DavidCas24/Adaptive_Telework_Environment/HARDWARE/Prototipo.png

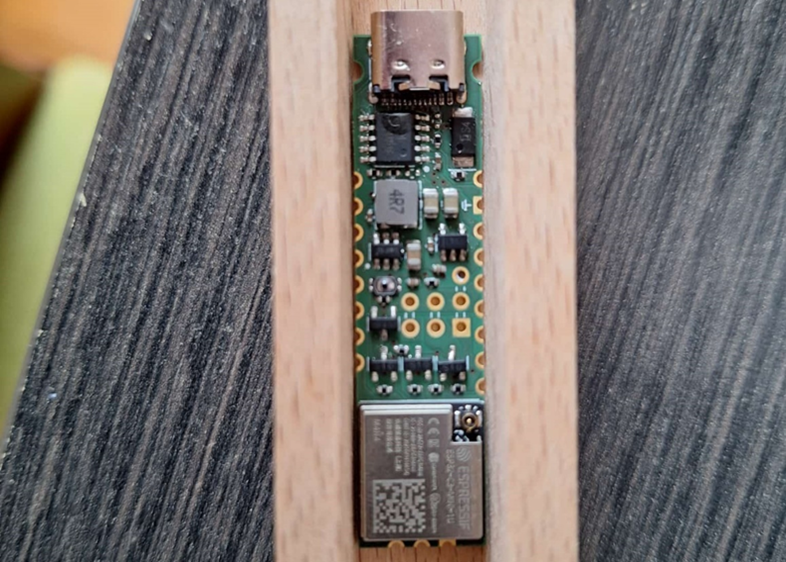
HARDWARE/Prototipo.png
