DavidCas24/Adaptive_Telework_Environment/PCB/3D/3D.png

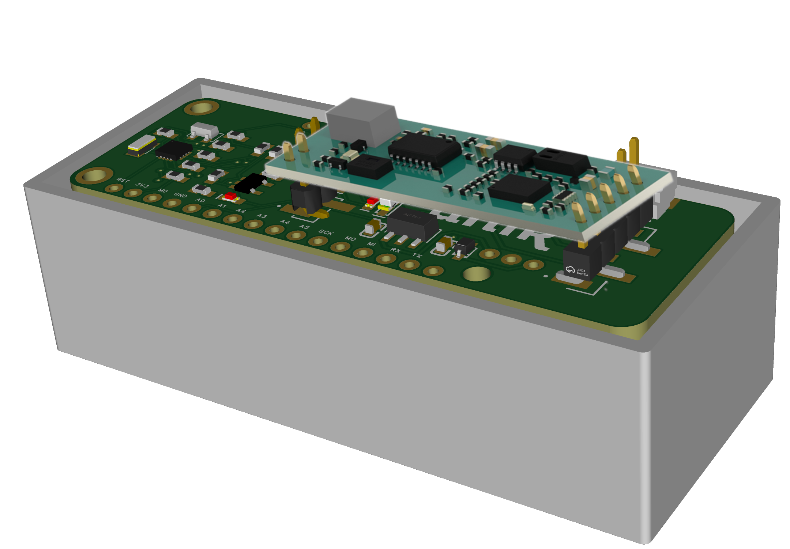
PCB/3D/3D.png
