DavidCas24/Adaptive_Telework_Environment/PCB/3D/3D_PCB_FeatherAB1805-SC_FINAL_2_2025-06-03_2025-06-03.png

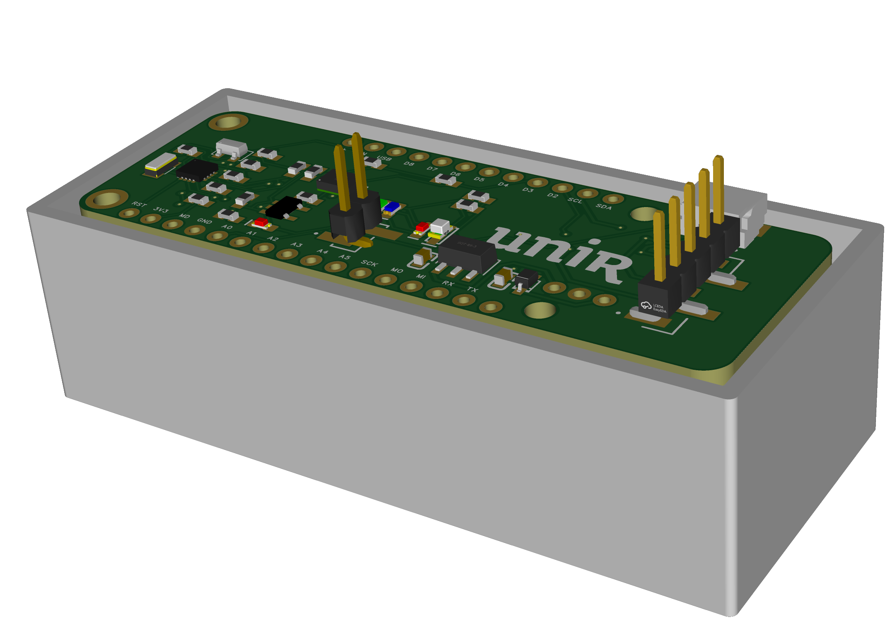
PCB/3D/3D_PCB_FeatherAB1805-SC_FINAL_2_2025-06-03_2025-06-03.png
