DavidCas24/Adaptive_Telework_Environment/PCB/3D/Ambimate - copia.png

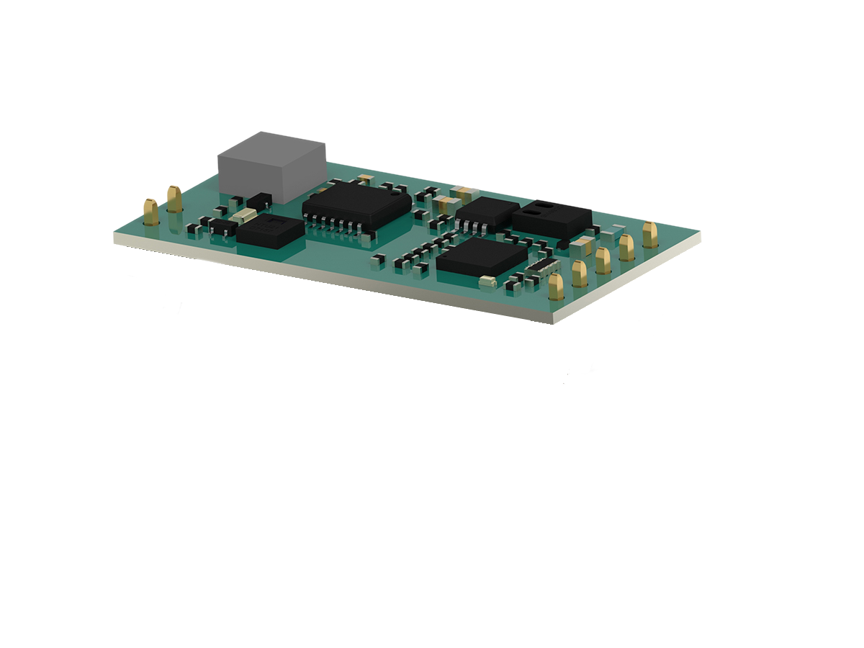
PCB/3D/Ambimate - copia.png
