DavidCas24/Adaptive_Telework_Environment/PCB/3D/PCB con envolvente.png

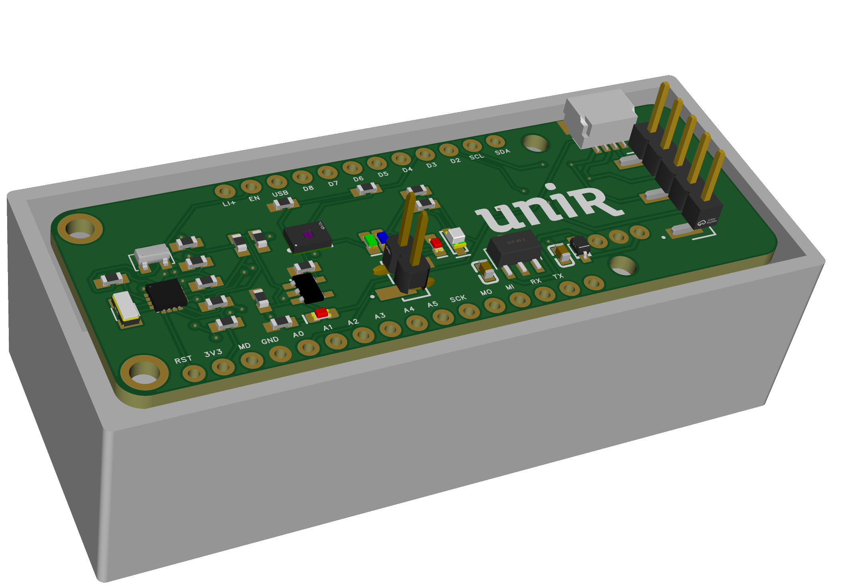
PCB/3D/PCB con envolvente.png
