DavidCas24/Adaptive_Telework_Environment/PCB/PARTICLE.IO SENSOR SHIELD PCB/MECHANICAL Modelo 3D/FreeCAD.jpg

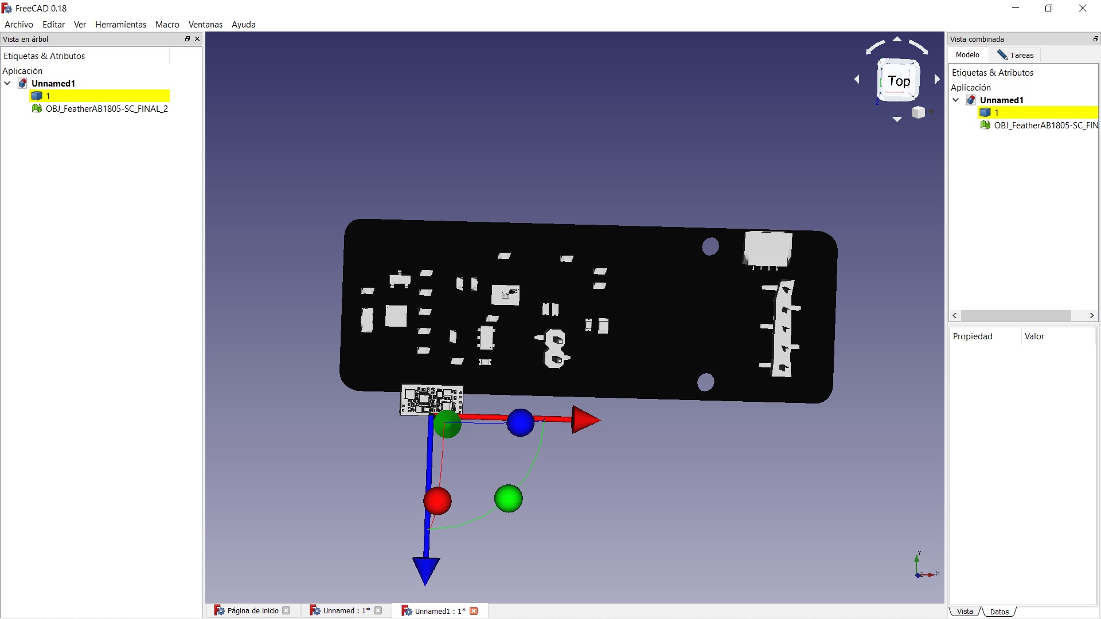
PCB/PARTICLE.IO SENSOR SHIELD PCB/MECHANICAL Modelo 3D/FreeCAD.jpg
