DavidCas24/Adaptive_Telework_Environment/PCB/PARTICLE.IO SENSOR SHIELD PCB/Tarjeta sensor LURMIS Featherwing/PCB_UNIR_3D.jpg

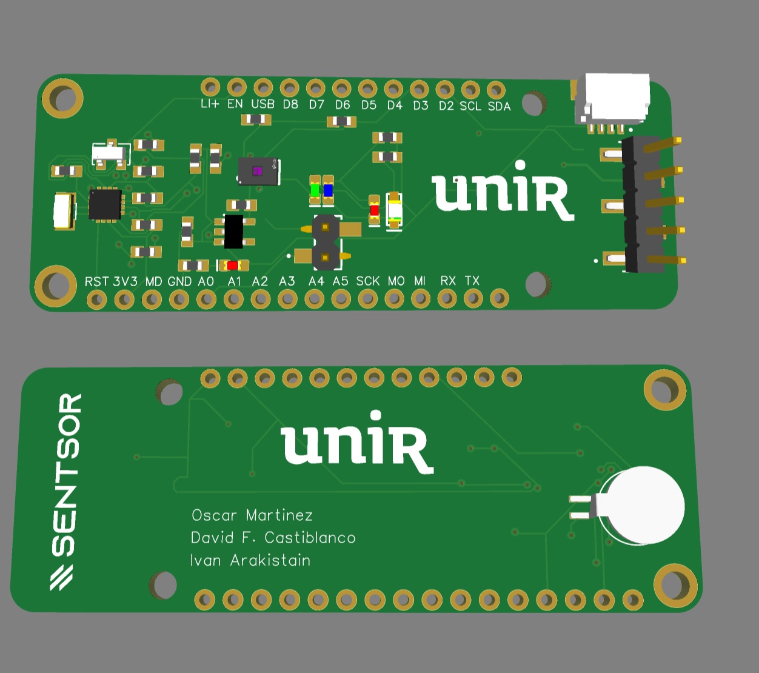
PCB/PARTICLE.IO SENSOR SHIELD PCB/Tarjeta sensor LURMIS Featherwing/PCB_UNIR_3D.jpg
